smvumbaco/Fitolux-FA24/production/src/fitolux-fw/include/MotorController.h

#ifndef MOTORCONTROLLER_H
#define MOTORCONTROLLER_H

#include <Arduino.h>

class MotorController {
public:
    MotorController();
    void setDirection(bool direction);
    void setSpeed(int speed);
    void enable();
    void disable();
    bool getState();

private:
    int standbyPin;
    int pwmPin;
    int in1Pin;
    int in2Pin;
    bool direction;
    int speed;
};

#endif
