smvumbaco/Fitolux-FA24/production/src/fitolux-fw/include/PortScreenHome.h

#pragma once

#ifndef _PORT_SCREEN_H
#define _PORT_SCREEN_H
#include <TFT_eSPI.h>
#include <Arduino.h>


// Declare external TFT object to ensure no redefinition
extern TFT_eSPI tft;
extern int batteryLevel;

// Function declarations
// void displayStartScreen();
void displayPortHomeScreen(TFT_eSPI &tft);
void updateValue(TFT_eSPI tft, int value, int battery);
// void updateWeightDisplay(int weight);
// void drawDispensingScreen();
// void drawCompleteScreen();
#endif
