smvumbaco/Fitolux-FA24/production/src/fitolux-fw/include/colors.h

#ifndef _COLORS_H_
#define _COLORS_H_
// Define colors in RGB565
#define COLOR_BROWN 0x8A22      // Brown in RGB565
#define COLOR_LIGHT_BROWN 0xF1EE // Background
#define COLOR_DARK_BROWN 0x8273  // Outer circle
#define COLOR_MEDIUM_BROWN 0xB19D // Middle circle
#define COLOR_LIGHTER_BROWN 0xD3C2 // Inner circle
#define COLOR_BLACK 0x0000          // Text color
#define COLOR_LIGHTEST_BROWN 0xEADC // Lighter Brown
#endif
